CoolNamesAllTaken/high-side-switch/ltspice/switch_tran.asc

C1: cap; 100µ
C2: cap; 1µ
C3: cap; 1µ
C4: cap; 100n
D1: diode; VS-E5PH3006
D2: zener; BZX84C10L
D3: zener; BZX84C10L
L1: ind; 5m
M1: pmos; RSJ250P10
M2: pmos; RSJ250P10
M3: nmos; 2n7002
M4: pmos; BSS84
M5: pmos
M6: pmos
Q1: npn; 2N5550
Q2: npn; 2N5550
Q3: pnp; 2N5401
R1: res; 6
R2: res; 200
R3: res; 1k
R4: res; 100
R5: res; 10k
R6: res; 1m
R7: res; 34
R8: res; 500
R9: res; 4.99k
R10: res; 10k
R11: res; 200k
R12: res; 1
R13: res; 10k
R14: res; 7.9k
R15: res; 10k
R16: res; 66.8k
R17: res; 19k
R18: res; 1k
R20: res; 10k
R21: res; 1.3k
R22: res; 1k
R23: res; 34k
R24: res; 1k
R25: res; 30k
R26: res; 1k
R27: res; 50k
R28: res; 1k
R29: res; 1k
R30: res; 10k
R31: res; 40k
R32: res; 1k
R33: res; 1k
R34: res; 10k
R35: res; 40k
R36: res; 10Meg
R37: res; 10k
R38: res; 10k
R39: res; 10k
R40: res; 50k
U1: LTC6102
U2: UniversalOpAmp2
U3: UniversalOpAmp2
U4: UniversalOpAmp2
U5: UniversalOpAmp2
U6: UniversalOpAmp2
U7: UniversalOpAmp2
U8: UniversalOpAmp2
U9: UniversalOpAmp2
V1: voltage; 60
V2: voltage; PULSE(0 3.3 10m 1n 1n 10m 20m 1)
V3: voltage; 5
V4: voltage; PULSE(0 100 225m 200m 10m 5 10)
V5: voltage; PULSE(0 3.3 25m 1n 1n 1 1.5 1)
V6: voltage; PULSE(0 -120 50m 10m 10m 30m 100m 1)
V7: voltage; PULSE(0 200 130m 10m 10m 30m 60m 1)
Named nets: 0, v_supply, enable, v_csense, 5v, v_oc_slow_delay, v_oc_fast_delay, v_vsense, v_uvlo, v_oc_fast, v_oc_slow, fault, fault_latched
Reverse Polarity Protection
High Side Switch
Load
Current Sense
.tran 0 500m 0 1u startup
Slow Overcurrent Protection
Fast Overcurrent Protection
Current Limited Zener Drive
R8 limits Zener current.
R2 dissipates power to preserve Q1.
Enable test pulse.
Enable hold ON for remaining testing.
Reverse polarity pulse.
Overvoltage slow ramp.
DC supply.
M3 protects v_vsense from overvoltage by limiting it to
5V-V_t, where V_t is threshold voltage of MOSFET.
Voltage divider and
lowpass filter.
Overvoltage fast pulse.
Shared Fault Bus with Time Delay Latch
